ecosdelunderground/lamparas/cortes_piezas.png

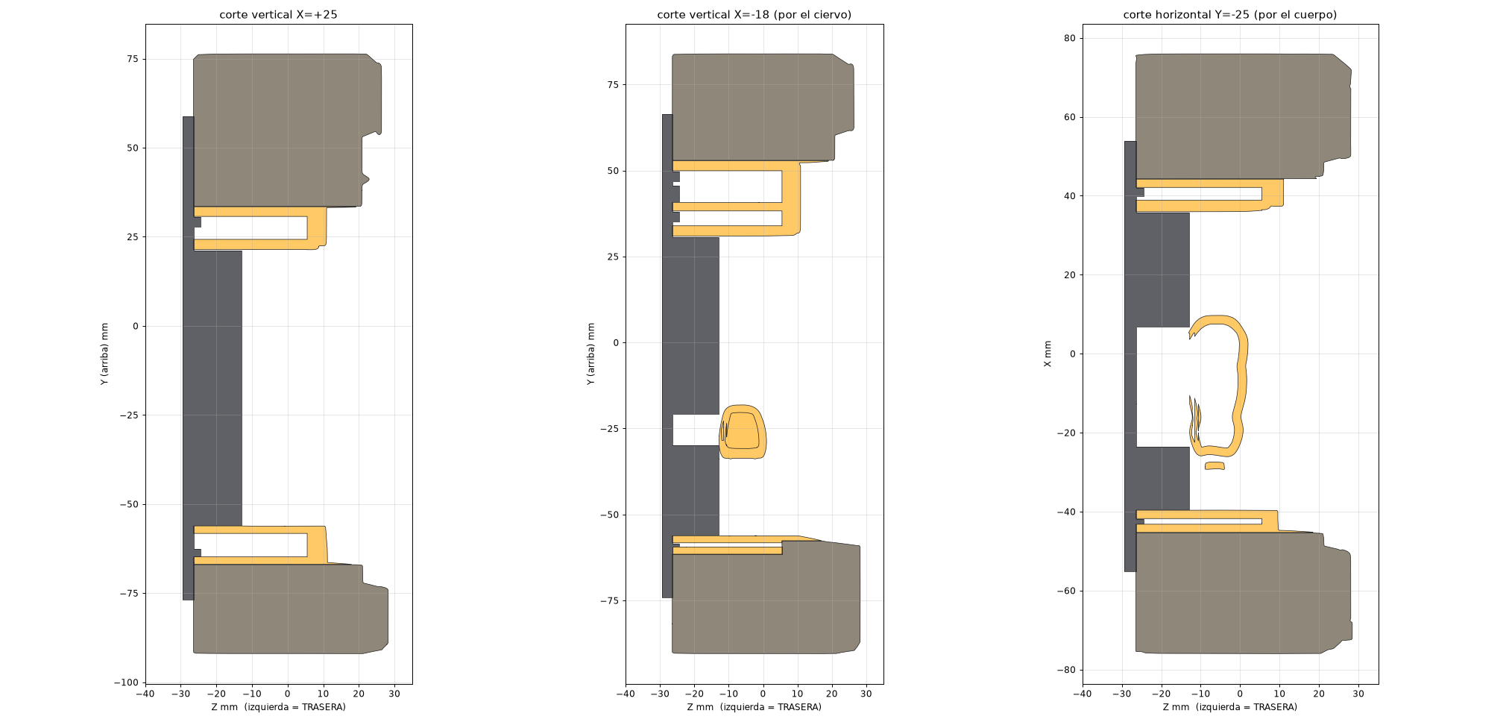
cortes_piezas.png
