ecosdelunderground/lamparas/despiece.png

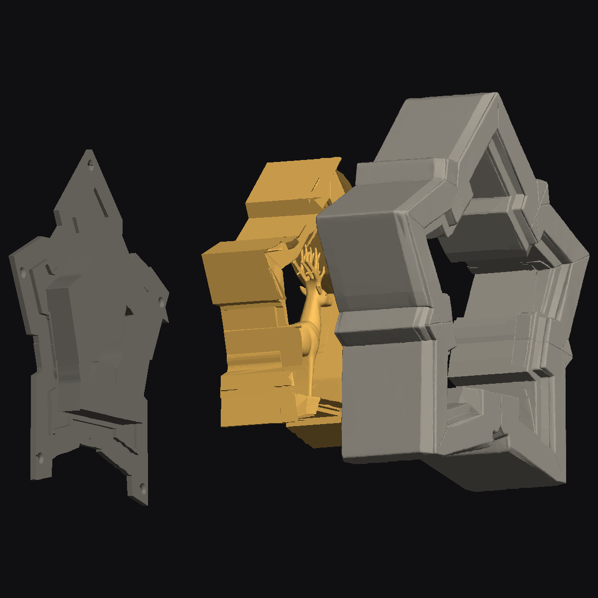
despiece.png
