ecosdelunderground/lamparas/esquema_pasillo.png

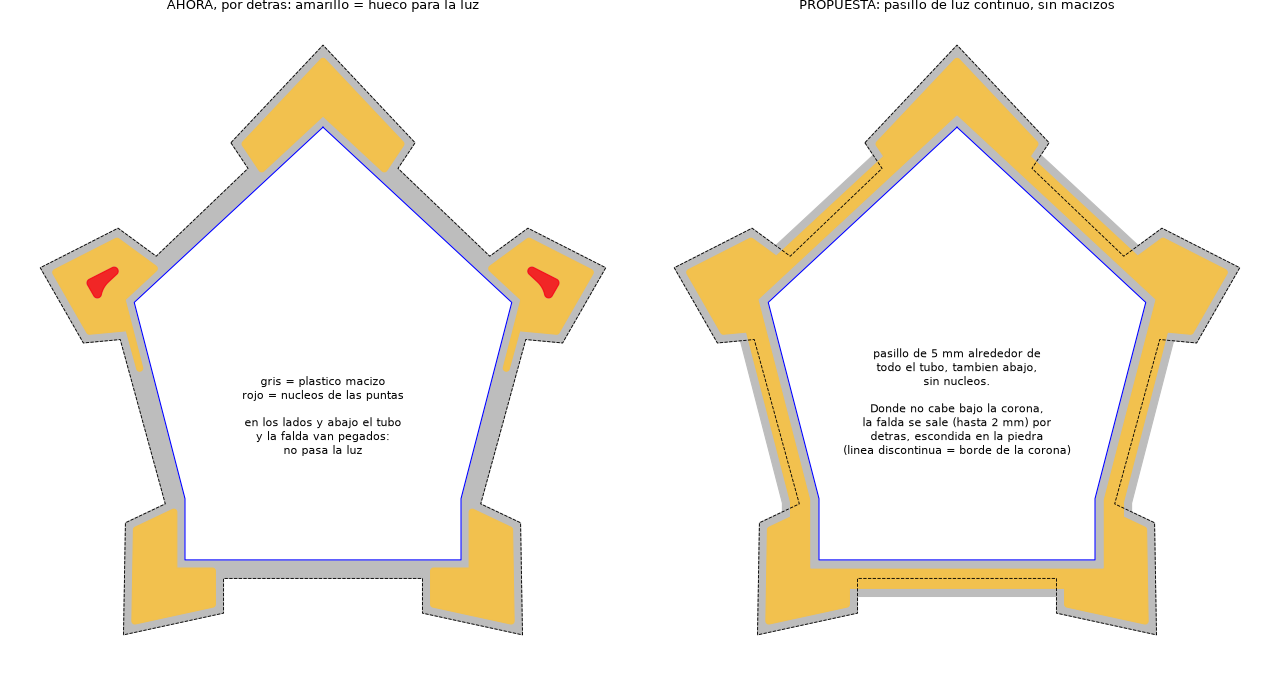
esquema_pasillo.png
