ecosdelunderground/lamparas/verificacion.png

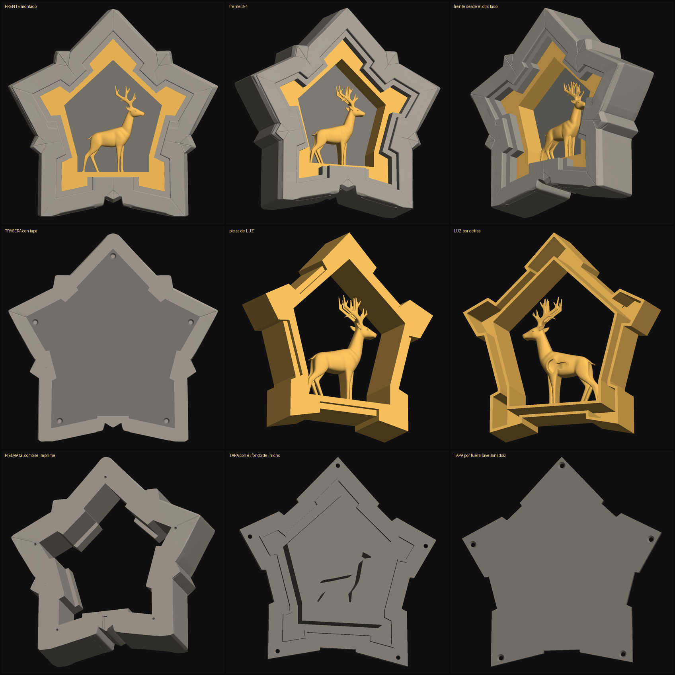
verificacion.png
